KavijaK/FMCWRadar/Simulations/Video Filtering/fmcw fliter - Copy (2).asc

1.6k: res; 1.6k
C1: cap; 10n
C2: cap; 10n
C3: cap; 270p
C4: cap; 0.1n
C5: cap; 1µ
C6: cap; 0.1n
C7: cap; 1µ
C8: cap; 3n
C9: cap; 0.1n
C10: cap; 0.1n
C11: cap; 3.3n
C12: cap; 3.3n
C13: cap; 10n
C14: cap; 1µ
C15: cap; 100n
C16: cap; 1µ
C17: cap; 100n
R1: res; 49.9
R2: res; 49.9
R3: res; 360
R4: res; 3.6k
R5: res; 3.6k
R6: res; 2.4k
R7: res; 2.4k
R8: res; 8.2k
R9: res; 8.2k
R10: res; 680
R11: res; 680
R12: res; 470
R13: res; 470
R16: res; 49.9
R17: res; 49.9
R18: res; 49.9
R19: res; 1.5k
R20: res; 27
R21: res; 120k
R_: res; 1.6k
U4: INA849
U5: THS4561
U6: THS4561
V1: voltage; 0; AC 1
V2: voltage; 5
V3: voltage; 5
Named nets: 0, V_cc, V_ee
.ac dec 300 10 1000k
