KavijaK/FMCWRadar/Simulations/Video Filtering/fmcw fliter - Copy.asc

2n: cap; 1n
C1: cap; 0.1n
C2: cap; 1n
C3: cap; 10n
C4: cap; 1n
C5: cap; 2.4n
C7: cap; 1µ
C8: cap; 2.4n
C9: cap; 1n
C13: cap; 10n
C14: cap; 1µ
C15: cap; 100n
C16: cap; 1µ
C17: cap; 100n
R1: res; 49.9
R2: res; 49.9
R3: res; 1k
R4: res; 4.99k
R5: res; 4.99k
R6: res; 422
R7: res; 49.9
R8: res; 49.9
R10: res; 1k
R19: res; 1.5k
R20: res; 27
R21: res; 120k
U4: INA849
U5: THS4561
V1: voltage; 0; AC 1
V2: voltage; 5
V3: voltage; 5
Named nets: 0, V_cc, V_ee
.ac dec 300 10 10000k
