KavijaK/FMCWRadar/Firmware/firmware/Core/Inc/adf4158.h

#ifndef ADF4158_H
#define ADF4158_H

void ADF4158_Init(void);
void ADF4158_Program(void);
void ADF4158_ProgramBladeRfTest(void);
void ADF4158_ProgramFastChirpTest(void);
void ADF4158_EnableRfOutput(void);

#endif /* ADF4158_H */
